llextv/DMXEasy/assets/AssemblageDMXEasy.step

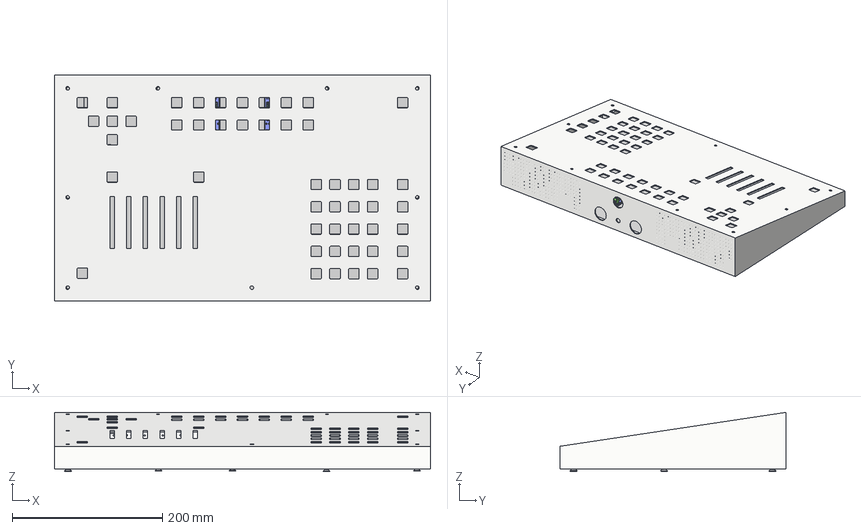
[picture p2: CAD file, 2026-08-04]
assets/AssemblageDMXEasy.step
500.0 x 300.0 x 78.7 mm
ESP_block_DMXEasy x 2
MAX485_DMXEasy x 2
DMXEasy
ESP-WROOM-32
2 PIN - DG306-5 - PITCH 5 mm v1 x 2
Black Pin H 2.5mm-6mm-3mm x4 v1 x 4
MAX485CUA v1 x 2
cherry_mx_reference_2020 x 50
BottomDMXEasy
PN-EN ISO 7046-2 - M5x16 - H Acier 4.6 Standard x 9
